notisrac/LCDbackpack/LCDBackpackLib/LCDBackpackLib.h

#ifndef LCDBackpackLib_h
#define LCDBackpackLib_h

#include <inttypes.h>
#include "Print.h"

// commands
#define LCD_CLEARDISPLAY 0x01
#define LCD_RETURNHOME 0x02
#define LCD_ENTRYMODESET 0x04
#define LCD_DISPLAYCONTROL 0x08
#define LCD_CURSORSHIFT 0x10
#define LCD_FUNCTIONSET 0x20
#define LCD_SETCGRAMADDR 0x40
#define LCD_SETDDRAMADDR 0x80

// flags for display entry mode
#define LCD_ENTRYRIGHT 0x00
#define LCD_ENTRYLEFT 0x02
#define LCD_ENTRYSHIFTINCREMENT 0x01
#define LCD_ENTRYSHIFTDECREMENT 0x00

// flags for display on/off control
#define LCD_DISPLAYON 0x04
#define LCD_DISPLAYOFF 0x00
#define LCD_CURSORON 0x02
#define LCD_CURSOROFF 0x00
#define LCD_BLINKON 0x01
#define LCD_BLINKOFF 0x00

// flags for display/cursor shift
#define LCD_DISPLAYMOVE 0x08
#define LCD_CURSORMOVE 0x00
#define LCD_MOVERIGHT 0x04
#define LCD_MOVELEFT 0x00

// flags for function set
#define LCD_8BITMODE 0x10
#define LCD_4BITMODE 0x00
#define LCD_2LINE 0x08
#define LCD_1LINE 0x00
#define LCD_5x10DOTS 0x04
#define LCD_5x8DOTS 0x00

// Shift register bits connected to LCD control pins
#define BACKLIGHT_BIT 0x04
#define RS_BIT 0x02
#define EN_BIT 0x08

// generic
#define MODE_INIT 0xFF
#define MODE_COMMAND 0x0
#define MODE_WRITE 0x1

class LCDBackpackLib : public Print {
public:
	LCDBackpackLib(uint8_t srdata, uint8_t srclock, uint8_t srlatch);
	void begin(uint8_t cols, uint8_t lines);
	void begin(uint8_t cols, uint8_t lines, uint8_t font);
	void clear();
	void home();
	void noDisplay();
	void display();
	void noBlink();
	void blink();
	void noCursor();
	void cursor();
	void scrollDisplayLeft();
	void scrollDisplayRight();
	void leftToRight();
	void rightToLeft();
	void autoscroll();
	void noAutoscroll();
	void backlightOn();
	void backlightOff();
	void createChar(uint8_t, uint8_t[]);
	void setCursor(uint8_t, uint8_t);

#if defined(ARDUINO) && ARDUINO >= 100
	virtual size_t write(uint8_t);
#else
	virtual void write(uint8_t);
#endif

	void command(uint8_t);
private:
	void init(uint8_t srdata, uint8_t srclock, uint8_t srlatch);
	void shiftOutBits(uint8_t value);
	void send(uint8_t, uint8_t);
	uint8_t _srdata_pin;
	uint8_t _srclock_pin;
	uint8_t _srlatch_pin;

	uint8_t _displayfunction;
	uint8_t _displaycontrol;
	uint8_t _displaymode;
	uint8_t _numlines;
	uint8_t _cols;
	uint8_t _backlight;

};

#endif
